ceybers/numpad-lcd-encoders/images/photos/20220527-IMG_1330.jpg

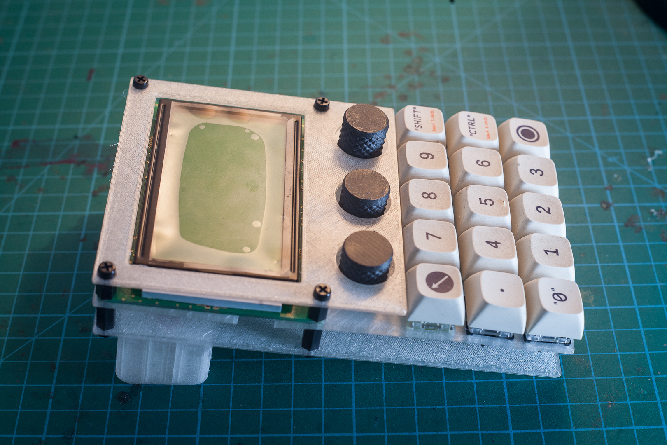
images/photos/20220527-IMG_1330.jpg
