ceybers/numpad-lcd-encoders/images/photos/20220527-IMG_1342.jpg

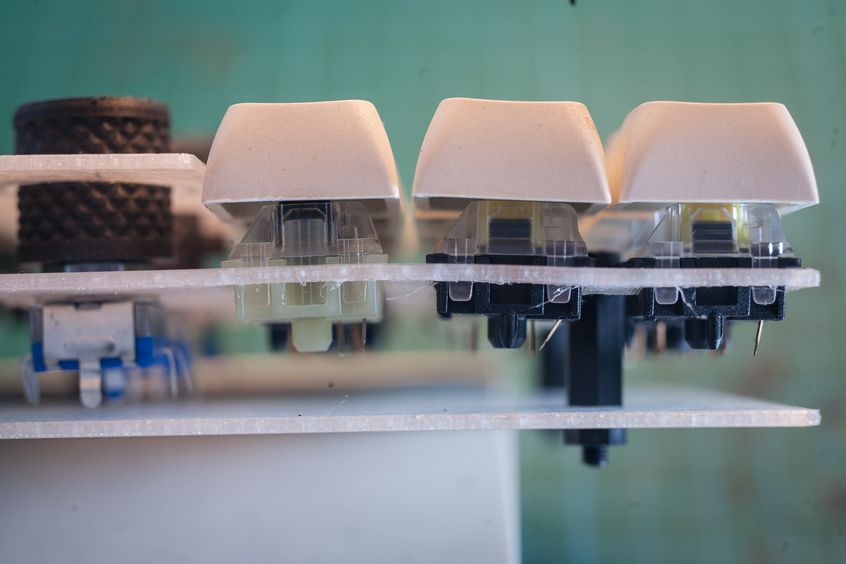
images/photos/20220527-IMG_1342.jpg
