ceybers/numpad-lcd-encoders/images/photos/20220530-IMG_1370.jpg

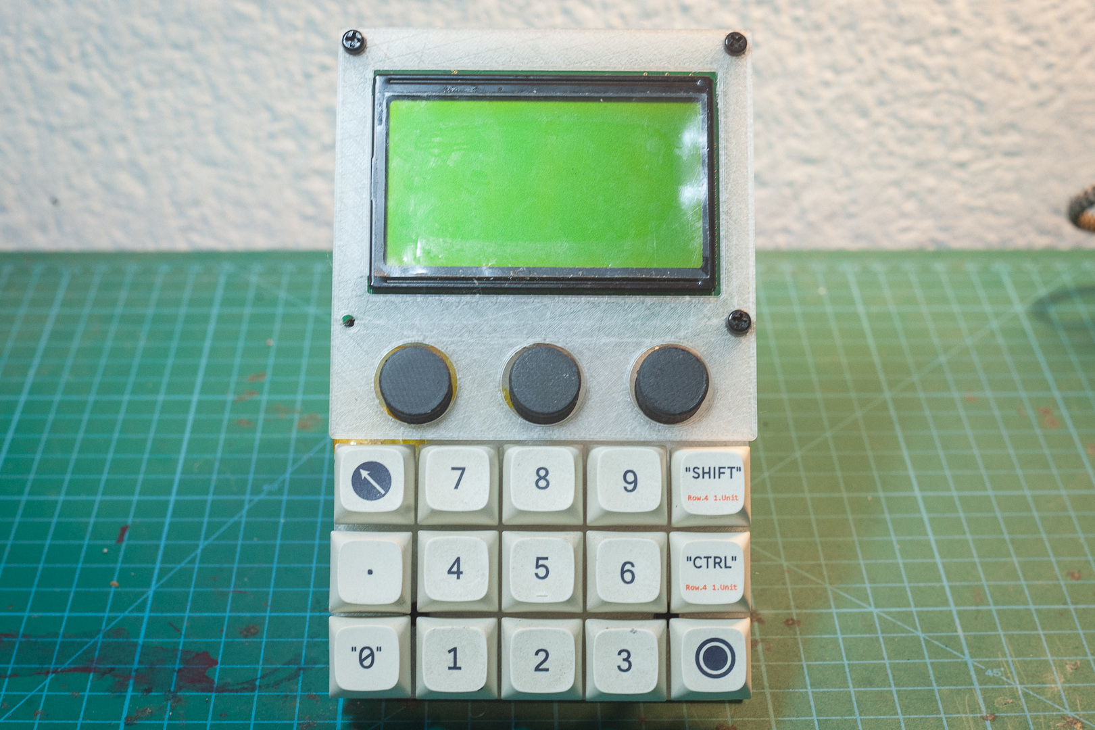
images/photos/20220530-IMG_1370.jpg
