ceybers/numpad-lcd-encoders/images/renders/Render-Opaque-Iso rev 3.png

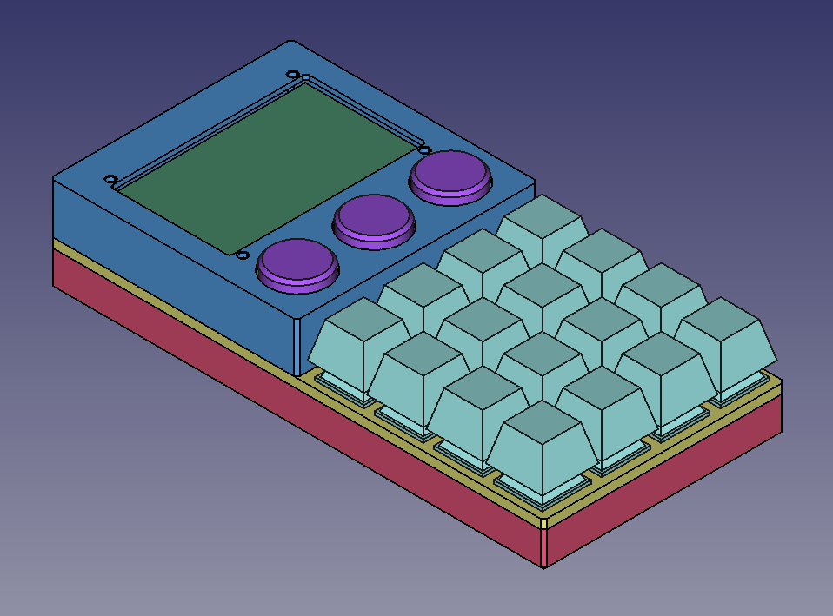
images/renders/Render-Opaque-Iso rev 3.png
