ceybers/numpad-lcd-encoders/images/renders/Render-Opaque-Iso.png

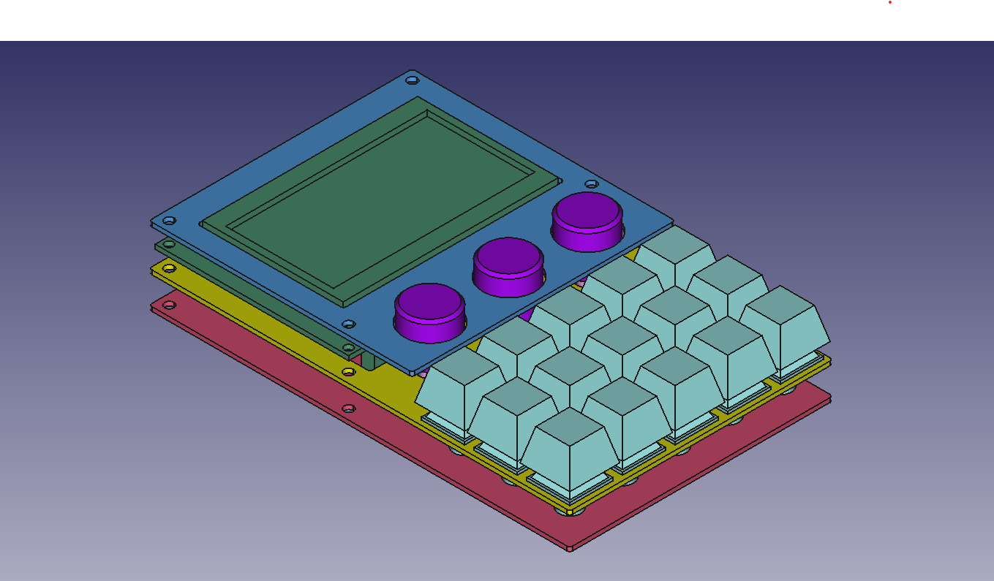
images/renders/Render-Opaque-Iso.png
