ceybers/numpad-lcd-encoders/images/renders/Render-Transparent-Iso.png

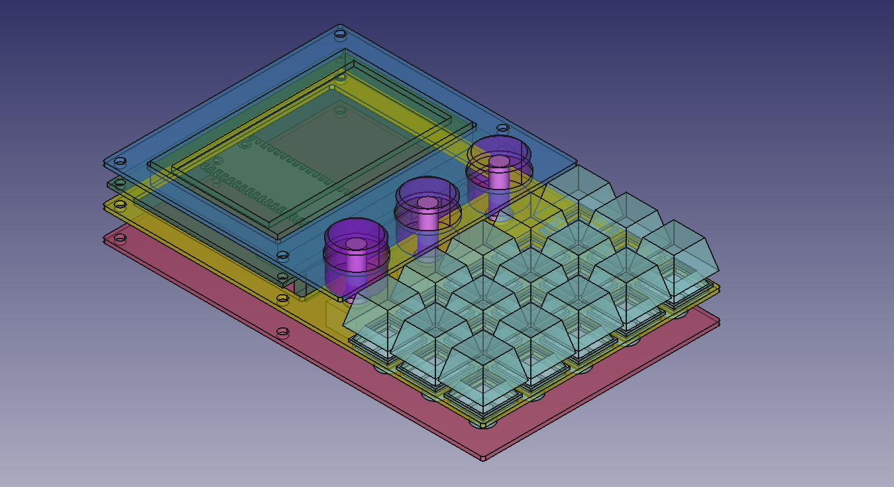
images/renders/Render-Transparent-Iso.png
